JibrilExe/PizzaPower/SolidModels/NoseConeV2.SLDPRT

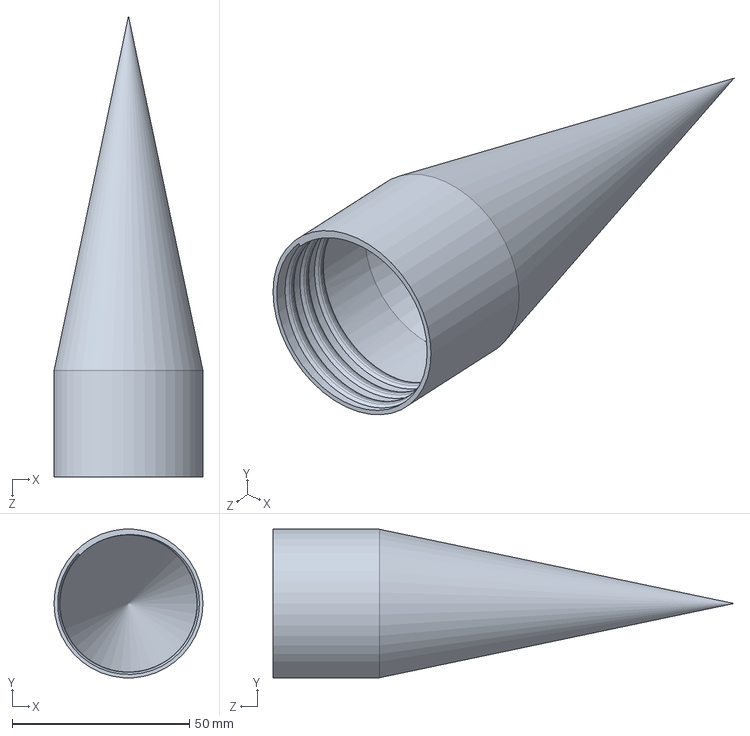
[picture p11: CAD file, 2026-06-06]
SolidModels/NoseConeV2.SLDPRT
42.0 x 41.9 x 130.0 mm
